osrf/ovc/ovc3/hardware/ovc3a/ovc3a/external_camera/README.md

# Lens holders
Lens holders have 20mm spacing. There are various options that work fine.
We have used PT-LH010M from m12lenses.com with good results:
https://www.m12lenses.com/CNC-Machined-M12-Lens-Holder-Metal-p/pt-lh010m.htm

# FFC jumpers
The required length of jumper depends on how the external-camera board is
mounted with respect to the main OVC3 board. We have used Molex 15266-0281
for 6" length (about 150mm) but many other alternatives are possible.
