osrf/ovc/docs/assets/images/ovc2-img2.png

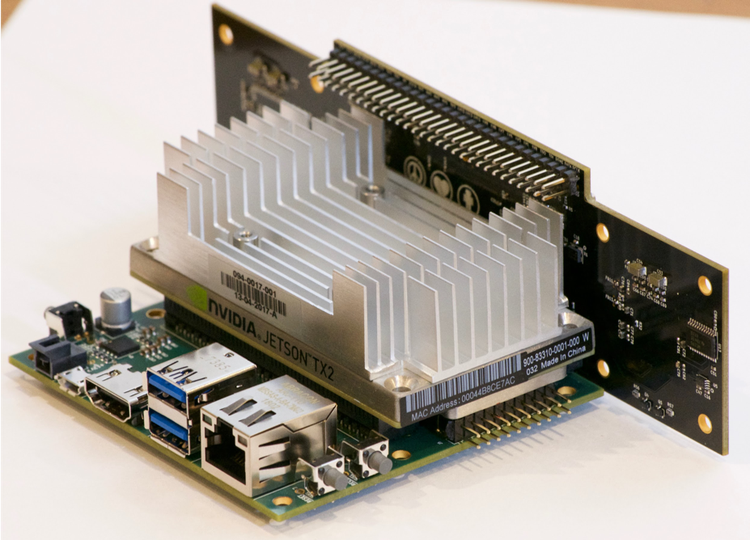
docs/assets/images/ovc2-img2.png
