osrf/ovc/ovc5/firmware/sandbox/10g_test/README.md

# sources
For lack of current understanding of the best way to put an enormous Vivado project into source control, we'll stash the files we've been editing here for safekeeping, and figure out a better system later.
