osrf/ovc/ovc5/software/clocking/configure_clock_generator.py

#!/usr/bin/env python3
import smbus
import sys
from time import sleep


SI5338_DEV_ADDR = 0x70


SI5338_CONFIG = [
    (  6, 0x08),  # mask bit for loss of signal (not needed?)
    ( 27, 0x00),  # confirm that reference voltage is 3.3v (not needed?)
    ( 28, 0x0b),  # use clock input IN3
    ( 29, 0x4a),  # use divide IN3 by 4, use P1DIV_OUT
    ( 30, 0xb0),  # no PDF_IN_FB, no clock into P2 divider
    ( 31, 0xe3),  # no clock into R0 divider, power down CLK0 driver
    ( 32, 0xe3),  # no clock into R1 divider, power down CLK1 driver
    ( 33, 0xe3),  # no clock into R2 divider, power down CLK2 driver
    ( 34, 0xc0),  # use MultiSynth3 output, set R3 divider to 1, power up CLK3
    ( 35, 0x00),  # all VDDO are connected to 3v3 on the board
    ( 36, 0x00),  # CLK0 is powered down
    ( 37, 0x00),  # CLK1 is powered down
    ( 38, 0x00),  # CLK2 is powered down
    ( 39, 0x06),  # CLK3 is LVDS
    ( 40, 0x63),  # trim bits, set by ClockBuilder
    ( 41, 0x0c),  # trim bits, set by ClockBuilder
    ( 42, 0x23),  # trim bits, set by ClockBuilder
    ( 45, 0x00),  # frequency calibration override (?)
    ( 46, 0x00),  # frequency calibration override (?)
    ( 47, 0x14),  # frequency calibration override (?)
    ( 48, 0x3A),  # internal feedback path, charge pump current (ClockBuilder)
    ( 49, 0x00),  # do not use frequency calibration override
    ( 50, 0xC4),  # enable PLL, use calibration (ClockBuilder)
    ( 51, 0x07),  # multisynch phase error correction
    ( 52, 0x10),  # disable frequency inc/dec on MS0
    ( 53, 0x00),  # MS0 params
    ( 54, 0x00),  # MS0 params
    ( 55, 0x00),  # MS0 params
    ( 56, 0x00),  # MS0 params
    ( 57, 0x00),  # MS0 params
    ( 58, 0x00),  # MS0 params
    ( 59, 0x00),  # MS0 params
    ( 60, 0x00),  # MS0 params
    ( 61, 0x00),  # MS0 params
    ( 62, 0x00),  # MS0 params
    ( 63, 0x10),  # MS1 disable inc/dec
    ( 64, 0x00),  # MS1 params
    ( 65, 0x00),  # MS1 params
    ( 66, 0x00),  # MS1 params
    ( 67, 0x00),  # MS1 params
    ( 68, 0x00),  # MS1 params
    ( 69, 0x00),  # MS1 params
    ( 70, 0x00),  # MS1 params
    ( 71, 0x00),  # MS1 params
    ( 72, 0x00),  # MS1 params
    ( 73, 0x00),  # MS1 params
    ( 74, 0x10),  # MS2 disable inc/dec
    ( 75, 0x00),  # MS2 params
    ( 76, 0x00),  # MS2 params
    ( 77, 0x00),  # MS2 params
    ( 78, 0x00),  # MS2 params
    ( 79, 0x00),  # MS2 params
    ( 80, 0x00),  # MS2 params
    ( 81, 0x00),  # MS2 params
    ( 82, 0x00),  # MS2 params
    ( 83, 0x00),  # MS2 params
    ( 84, 0x00),  # MS2 params
    ( 85, 0x10),  # MS3 disable inc/dec
    ( 86, 0x00),  # MS3 params
    ( 87, 0x06),  # MS3 params
    ( 88, 0x00),  # MS3 params
    ( 89, 0x00),  # MS3 params
    ( 90, 0x00),  # MS3 params
    ( 91, 0x00),  # MS3 params
    ( 92, 0x01),  # MS3 params
    ( 93, 0x00),  # MS3 params
    ( 94, 0x00),  # MS3 params
    ( 95, 0x00),  # MS3 params
    ( 97, 0x00),  # MSN params
    ( 98, 0x30),  # MSN params
    ( 99, 0x00),  # MSN params
    (100, 0x00),  # MSN params
    (101, 0x00),  # MSN params
    (102, 0x00),  # MSN params
    (103, 0x01),  # MSN params
    (104, 0x00),  # MSN params
    (105, 0x00),  # MSN params
    (106, 0x80),  # MSN params
    (107, 0x00),  # MS0 phase offset
    (108, 0x00),  # MS0 phase offset
    (109, 0x00),  # MS0 phase step size
    (110, 0x40),  # clk0 output LOW when disabled
    (111, 0x00),  # MS1 phase offset
    (112, 0x00),  # MS1 phase offset
    (113, 0x00),  # MS1 phase step size
    (114, 0x40),  # CLK1 output LOW when disabled
    (115, 0x00),  # MS2 phase offset
    (116, 0x80),  # MS2 phase offset
    (117, 0x00),  # MS2 phase step size
    (118, 0x40),  # CLK2 output LOW when disabled
    (119, 0x00),  # MS3 phase offset
    (120, 0x00),  # MS3 phase offset
    (121, 0x00),  # MS3 phase step size
    (122, 0x00),  # CLK3 output high-Z when disabled
    (123, 0x00),  # MS0 inc/dec params
    (124, 0x00),  # MS0 inc/dec parmas
    (125, 0x00),  # MS0 inc/dec params
    (126, 0x00),  # MS0 inc/dec params
    (127, 0x00),  # MS0 inc/dec params
    (128, 0x00),  # MS0 inc/dec params
    (129, 0x00),  # MS0 inc/dec params
    (130, 0x00),  # MS0 inc/dec params
    (131, 0x00),  # MS0 inc/dec params
    (132, 0x00),  # MS0 inc/dec params
    (133, 0x00),  # MS0 inc/dec params
    (134, 0x00),  # MS0 inc/dec params
    (135, 0x00),  # MS0 inc/dec params
    (136, 0x00),  # MS0 inc/dec params
    (137, 0x00),  # MS0 inc/dec params
    (138, 0x00),  # MS0 inc/dec params
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
    (321, 0x01),  # MS2 spread spectrum params
    (322, 0x00),  # MS2 spread spectrum params
    (323, 0x00),  # MS2 spread spectrum params
    (324, 0x90),  # MS2 spread spectrum params
    (325, 0x31),  # MS2 spread spectrum params
    (326, 0x00),  # MS2 spread spectrum params
    (327, 0x00),  # MS2 spread spectrum params
    (328, 0x01),  # MS2 spread spectrum params
    (329, 0x00),  # MS2 spread spectrum params
    (330, 0x00),  # MS2 spread spectrum params
    (331, 0x00),  # MS2 spread spectrum params
    (335, 0x00),  # MS3 spread spectrum params
    (336, 0x00),  # MS3 spread spectrum params
    (337, 0x00),  # MS3 spread spectrum params
    (338, 0x00),  # MS3 spread spectrum params
    (339, 0x00),  # MS3 spread spectrum params
    (340, 0x90),  # MS3 spread spectrum params
    (341, 0x31),  # MS3 spread spectrum params
    (342, 0x00),  # MS3 spread spectrum params
    (343, 0x00),  # MS3 spread spectrum params
    (344, 0x01),  # MS3 spread spectrum params
    (345, 0x00),  # MS3 spread spectrum params
    (346, 0x00),  # MS3 spread spectrum params
    (347, 0x00),  # MS3 spread spectrum params
]


def si5338_set_page(bus, reg_addr):
    if reg_addr >= 256:
        page_idx = 1
    else:
        page_idx = 0
    bus.write_byte_data(SI5338_DEV_ADDR, 255, page_idx)


def si5338_translate_addr(reg_addr):
    if reg_addr >= 256:
        return reg_addr - 256
    else:
        return reg_addr


def si5338_write_allowed_mask(reg_addr):
    masks = [
        (  0, 0x00),
        (  1, 0x00),
        (  2, 0x00),
        (  3, 0x00),
        (  4, 0x00),
        (  5, 0x00),
        (  6, 0x1D),
        (  7, 0x00),
        (  8, 0x00),
        (  9, 0x00),
        ( 10, 0x00),
        ( 11, 0x00),
        ( 12, 0x00),
        ( 13, 0x00),
        ( 14, 0x00),
        ( 15, 0x00),
        ( 16, 0x00),
        ( 17, 0x00),
        ( 18, 0x00),
        ( 19, 0x00),
        ( 20, 0x00),
        ( 21, 0x00),
        ( 22, 0x00),
        ( 23, 0x00),
        ( 24, 0x00),
        ( 25, 0x00),
        ( 26, 0x00),
        ( 27, 0x80),
        ( 28, 0xFF),
        ( 29, 0xFF),
        ( 30, 0xFF),
        ( 31, 0xFF),
        ( 32, 0xFF),
        ( 33, 0xFF),
        ( 34, 0xFF),
        ( 35, 0xFF),
        ( 36, 0x1F),
        ( 37, 0x1F),
        ( 38, 0x1F),
        ( 39, 0x1F),
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
    ]
    for m in masks:
        if m[0] == reg_addr:
            return m[1]
    # if we get here, that means we didn't find one... bogus addr :(
    raise Exception("bad address! no mask!")


def si5338_set_register(bus, reg_addr, reg_val, set_page=True):
    if set_page:
        si5338_set_page(bus, reg_addr)

    mask = si5338_write_allowed_mask(reg_addr)
    #print(f'reg {reg_addr} mask = 0x{mask:02x}')

    if mask == 0xff:
        bus.write_byte_data(
            SI5338_DEV_ADDR,
            si5338_translate_addr(reg_addr),
            reg_val)
    else:
        # have to do a read-modify-write
        prev_val = si5338_get_register(bus, reg_addr, False)
        masked_prev_val = prev_val & ~mask
        masked_new_val = reg_val & mask
        bus.write_byte_data(
            SI5338_DEV_ADDR,
            si5338_translate_addr(reg_addr),
            masked_prev_val | masked_new_val)


def si5338_get_register(bus, reg_addr, set_page=True):
    if set_page:
        si5338_set_page(bus, reg_addr)

    return bus.read_byte_data(
        SI5338_DEV_ADDR,
        si5338_translate_addr(reg_addr))


def si5338_print_register(bus, reg_addr):
    val = si5338_get_register(bus, reg_addr)
    print(f'reg {reg_addr}: 0x{val:02x}')


def configure_clock_generator():
    bus = smbus.SMBus(0)  # clock generator is on the first i2c bus

    reg0 = si5338_get_register(bus, 0)  #bus.read_byte_data(SI5338_DEV_ADDR, 0)
    if reg0 != 1:
        print(f'unexpected value for Si5338 reg 0: {reg0}')
        sys.exit(1)

    print(f'successfully read Si5338 version register: {reg0}')

    # disable all outputs
    si5338_set_register(bus, 230, 0x10)

    # pause LOL by asserting high bit of reg 241
    si5338_set_register(bus, 241, 0xe5)

    # populate register table
    #si5338_set_register(bus, 2
    for reg in SI5338_CONFIG:
        reg_addr = reg[0]
        reg_val = reg[1]
        si5338_set_register(bus, reg_addr, reg_val)

    si5338_set_register(bus, 246, 0x02)  # start soft reset
    sleep(0.025)  # sleep at least 25ms

    # restart LOL
    si5338_set_register(bus, 241, 0x65)

    # check lock bits
    for i in range(0, 100):
        status = si5338_get_register(bus, 218)
        if status == 0x08:
            print('PLL locked, hooray')
            break
        else:
            print('waiting for lock...')

    # copy FCAL to active registers
    si5338_print_register(bus, 237)
    si5338_print_register(bus, 236)
    si5338_print_register(bus, 235)
    si5338_set_register(bus, 47, si5338_get_register(bus, 237) & 0x3)
    si5338_set_register(bus, 46, si5338_get_register(bus, 236))
    si5338_set_register(bus, 45, si5338_get_register(bus, 235))

    # enable FCAL
    si5338_set_register(bus, 49, si5338_get_register(bus, 49) | 0x80)

    # turn off global clock disable
    si5338_set_register(bus, 230, si5338_get_register(bus, 230) & ~0x10)

    # sanity check a few values
    si5338_print_register(bus, 230)
    si5338_print_register(bus, 218)

    # JUST FOR TESTING: power consumption: disable all clocks
    # si5338_set_register(bus, 230, 0xf)


if __name__ == '__main__':
    configure_clock_generator()
