osrf/ovc/ovc5/software/camera_device_driver/include/ovc5_driver/uio_driver.hpp

#ifndef UIO_DRIVER_H
#define UIO_DRIVER_H

#include <stddef.h>

class UIODriver
{
  const int IRQ_RST = 1;
  int uio_file;
  unsigned int *uio_mmap;

  unsigned int reset_register, reset_mask;

public:
  UIODriver(int uio_num, size_t map_size);

  void setResetRegisterMask(unsigned int reg_addr, unsigned int mask);

  unsigned int readRegister(int reg_addr) const;
  void writeRegister(int reg_addr, int value);

  bool waitInterrupt();
};
#endif
