osrf/ovc/ovc5/software/camera_device_driver/include/ovc5_driver/vdma_driver.h

#ifndef VDMA_DRIVER_H
#define VDMA_DRIVER_H

#include <ovc5_driver/uio_driver.hpp>
#include <string>
#include <vector>

class VDMADriver
{
  // Register addresses
  const int VDMACR = 0x30 / sizeof(int);
  const int VDMASR = 0x34 / sizeof(int);
  const int VSIZE_REG = 0xA0 / sizeof(int);
  const int HSIZE_REG = 0xA4 / sizeof(int);
  const int FRMDLY_STRIDE_REG = 0xA8 / sizeof(int);
  const int PARK_PTR_REG = 0x28 / sizeof(int);
  const int START_ADDR_0 = 0xAC / sizeof(int);

  static constexpr int NUM_FRAMEBUFFERS = 4;

  const size_t UIO_SIZE = 0x1000;
  // UIO is for AXI4 lite configuration, memory is to access DDR and images
  UIODriver uio;

  unsigned char* memory_mmap[NUM_FRAMEBUFFERS];
  int sync_fd[NUM_FRAMEBUFFERS];

  void startVDMA(int res_y);
  std::pair<size_t, size_t> readFramebuffer(const std::string& buffer_name);
  void sendFramebuffer(int fb_num, uint32_t address);

  void updateLastFramebuffer(int frame_offset);

  int last_fb;

public:
  void setHeader(const std::vector<uint8_t>& header, int index = -1);

  void configureVDMA(int res_x, int res_y, int bit_depth,
                     bool enable_interrupt = true);

  VDMADriver(int uio_num, int cam_id);
  unsigned char* getImage(int frame_offset);
  unsigned char* getImageNoInterrupt(int frame_offset);

  void flushCache();
};
#endif
