osrf/ovc/ovc2/software/modules/ovc2_core/ovc2_core.c

#include <linux/cdev.h>
#include <linux/device.h>
#include <linux/delay.h>
#include <linux/fs.h>
#include <linux/init.h>
#include <linux/interrupt.h>
#include <linux/irq.h>
//#include <linux/io.h>
#include <linux/module.h>
#include <linux/moduleparam.h>
#include <linux/pci.h>
#include <asm/spinlock.h>
#include <linux/uaccess.h>
#include "ovc2_ioctl.h"
//#include <linux/uaccess.h>

static unsigned short vid = 0x1234;
static unsigned short did = 0x5678;
module_param(vid, ushort, S_IRUGO);
module_param(did, ushort, S_IRUGO);
#define OVC2_CHRDEV_REGION_NAME "ovc2"
#define OVC2_CHRDEV_COUNT 3
#define OVC2_MINOR_CORE 0
#define OVC2_MINOR_IMU  1
#define OVC2_MINOR_CAM  2

#define OVC2_CAM_DMA_BUF_SIZE (4*1024*1024)
struct ovc2_core {
  struct cdev cdev_core, cdev_imu, cdev_cam;
  int major;  // will be populated by alloc_chrdev_region()
  struct pci_dev *pci_dev;
  void __iomem *bar0_addr, *bar2_addr, *bar3_addr;
  atomic_t is_available;
  struct class *dev_class;
  struct device *device;
  struct completion cam_done, imu_done;
  struct ovc2_imu_data imu_data;
  uint8_t *cam_dma_buf;
  dma_addr_t cam_dma_addr;
};
static struct ovc2_core ovc2_core;
//////////////////////////////////////////////////////////////////////
DEFINE_SPINLOCK(pio_spinlock);
//////////////////////////////////////////////////////////////////////

int ovc2_core_open(struct inode *inode, struct file *fp)
{
  //printk(KERN_INFO "ovc2_core_open()\n");
  if (!atomic_dec_and_test(&ovc2_core.is_available)) {
    atomic_inc(&ovc2_core.is_available);
    return -EBUSY;
  }
  return 0;  // success  
}

int ovc2_core_release(struct inode *inode, struct file *file)
{
  //printk(KERN_INFO "ovc2_core_release()\n");
  atomic_inc(&ovc2_core.is_available);
  return 0;  // success
}

static long ovc2_cycle_bit(uint32_t reg_idx, uint8_t bit_idx)
{
  if (reg_idx == OVC2_REG_PCIE_PIO) {
    uint32_t pio_value;
    unsigned long flags;
    spin_lock_irqsave(&pio_spinlock, flags);
    pio_value = ioread32(ovc2_core.bar0_addr + 0x4000);
    iowrite32(pio_value | (1 << bit_idx), ovc2_core.bar0_addr + 0x4000);
    iowrite32(pio_value, ovc2_core.bar0_addr + 0x4000);
    spin_unlock_irqrestore(&pio_spinlock, flags);
  }
  else {
    // print warning message to kernel log? or just ignore?
  }
  return 0;
}
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
